b-wave/uDSKY/Files/20161008_122015.jpg

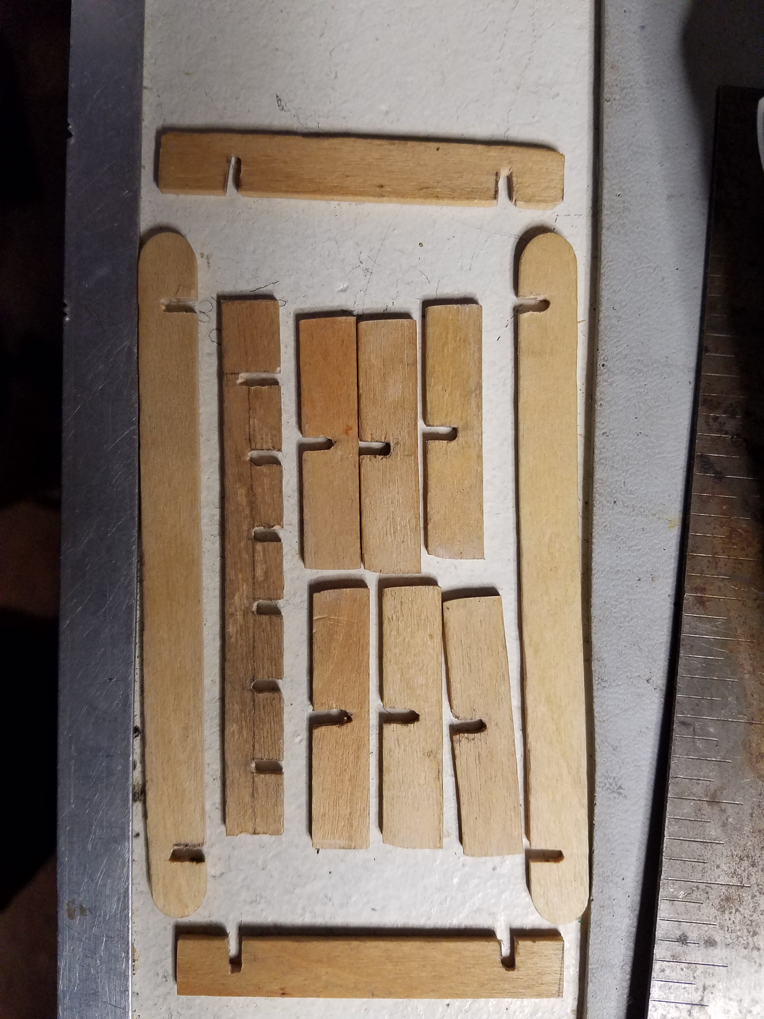
Files/20161008_122015.jpg
