b-wave/uDSKY/Files/20161217_135148.jpg

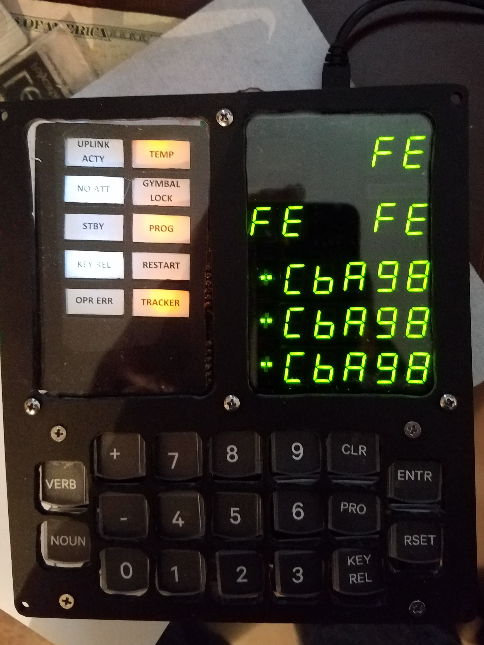
Files/20161217_135148.jpg
