b-wave/uDSKY/Files/20161217_135218.jpg

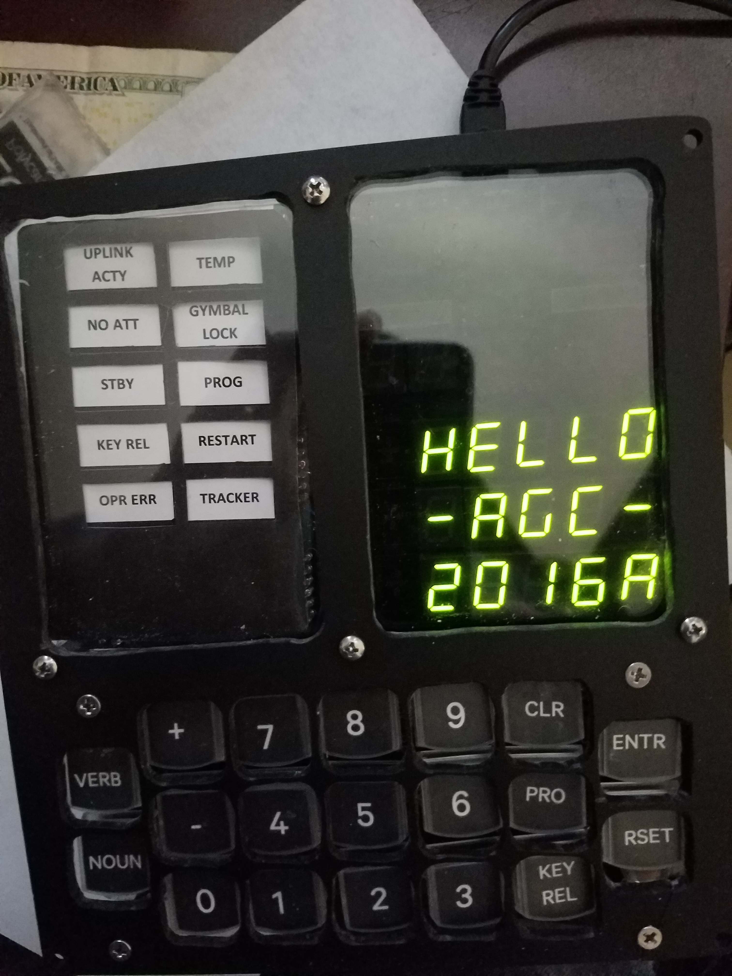
Files/20161217_135218.jpg
