b-wave/uDSKY/uDSKY Hardware/DSKY_DISP/DS_PLUS Files/DS_PLUS Files/20170219_095406.jpg

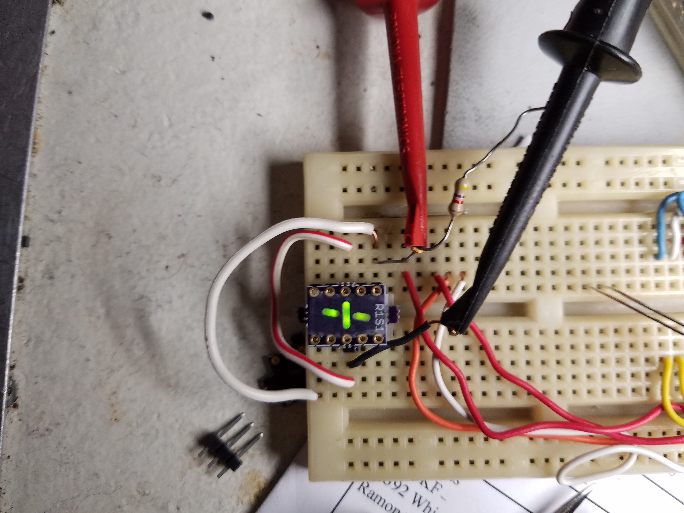
uDSKY Hardware/DSKY_DISP/DS_PLUS Files/DS_PLUS Files/20170219_095406.jpg
