b-wave/uDSKY/uDSKY IMU/apollo4/data/asm01.jpg

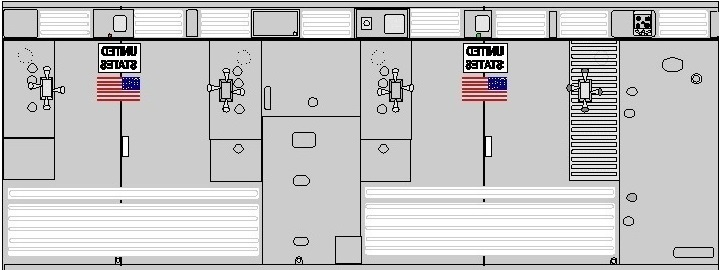
uDSKY IMU/apollo4/data/asm01.jpg
