b-wave/uDSKY/uDSKY IMU/apollo4/data/asm02.jpg

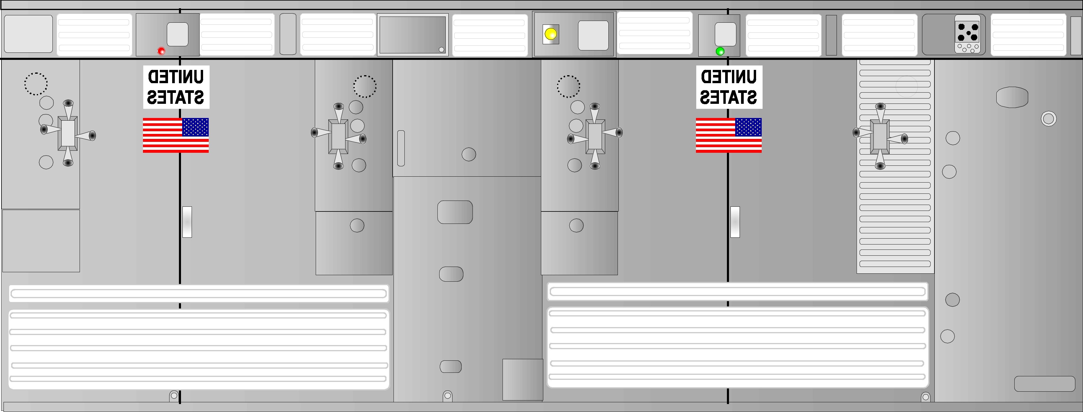
uDSKY IMU/apollo4/data/asm02.jpg
