b-wave/uDSKY/uDSKY IMU/apollo4/data/CM2b.JPG

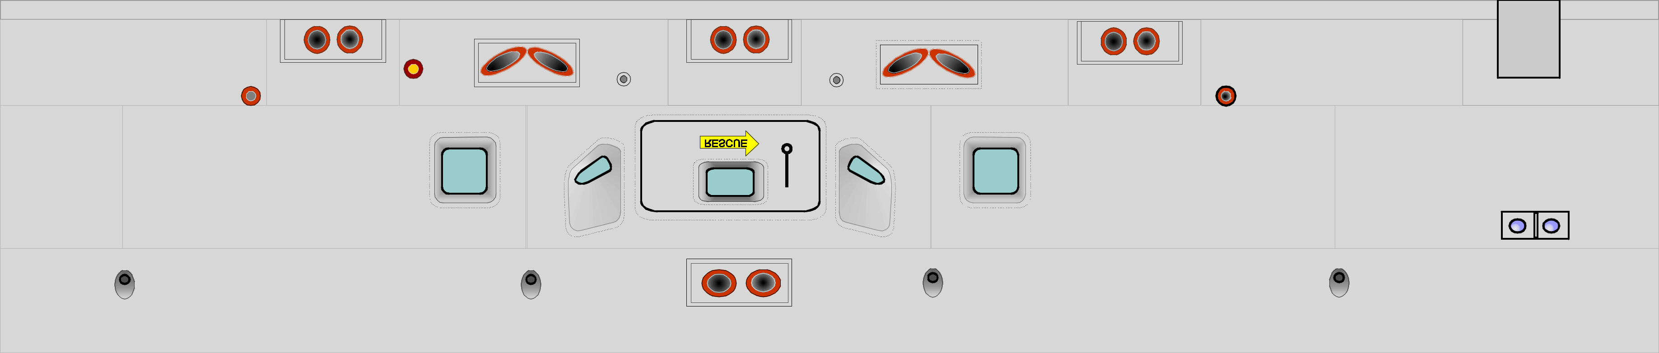
uDSKY IMU/apollo4/data/CM2b.JPG
