b-wave/uDSKY/uDSKY IMU/apollo4/data/CM2d.JPG

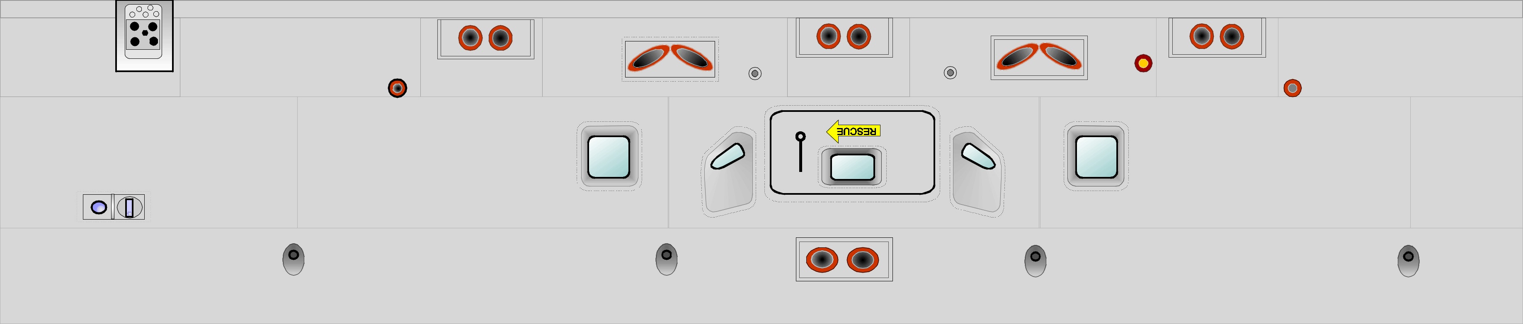
uDSKY IMU/apollo4/data/CM2d.JPG
