b-wave/uDSKY/uDSKY IMU/Apollo_FDAI_IMU1/data/fadi_texture_sb.png

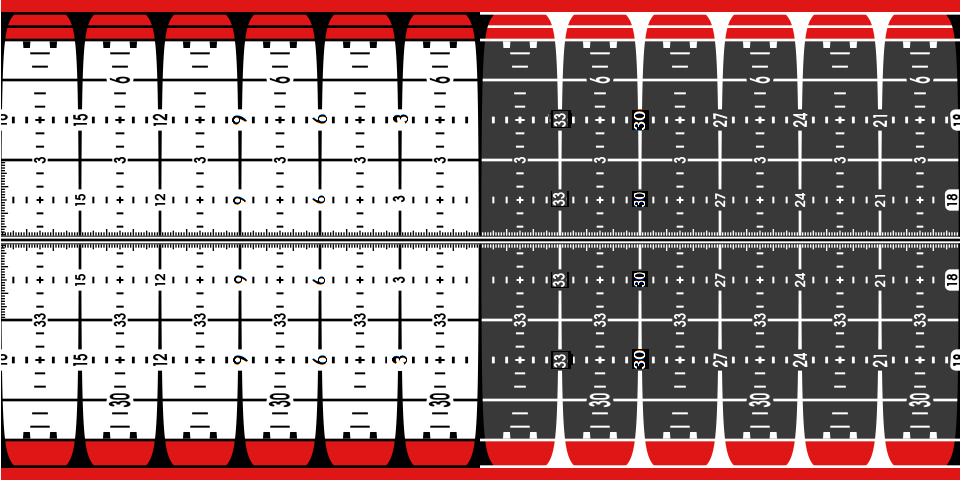
uDSKY IMU/Apollo_FDAI_IMU1/data/fadi_texture_sb.png
