b-wave/uDSKY/uDSKY IMU/Apollo_FDAI_IMU1/data/MLSM-lm8panel.jpg

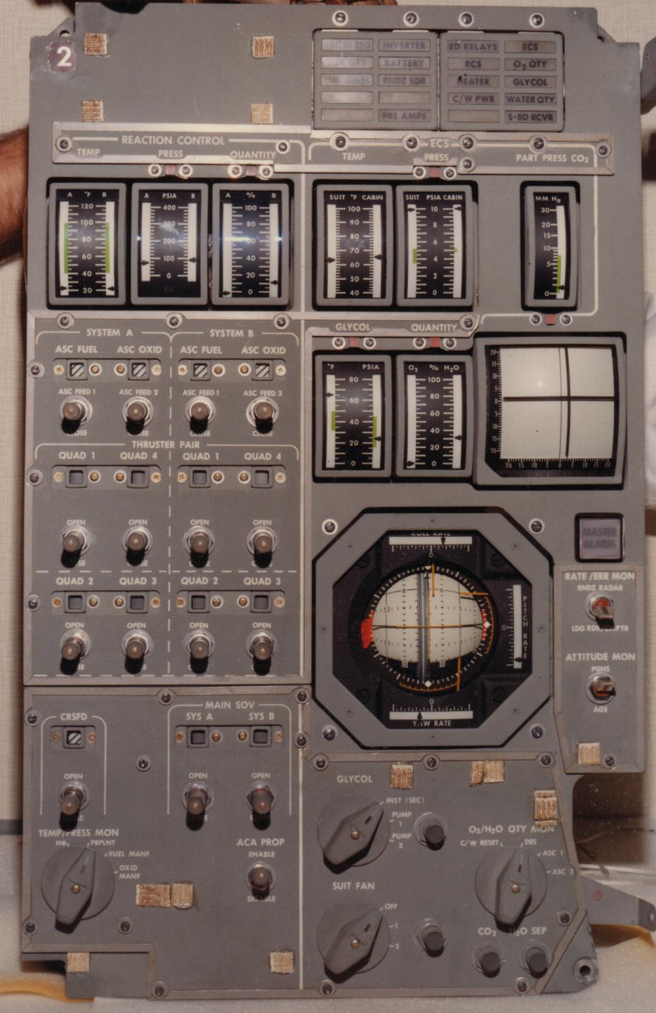
uDSKY IMU/Apollo_FDAI_IMU1/data/MLSM-lm8panel.jpg
